tanaydhavate/ODT2026-CapstoneProjectName-Tanay/Media/Week1/WhatsApp Image 2026-04-22 at 2.16.44 AM (1).jpeg

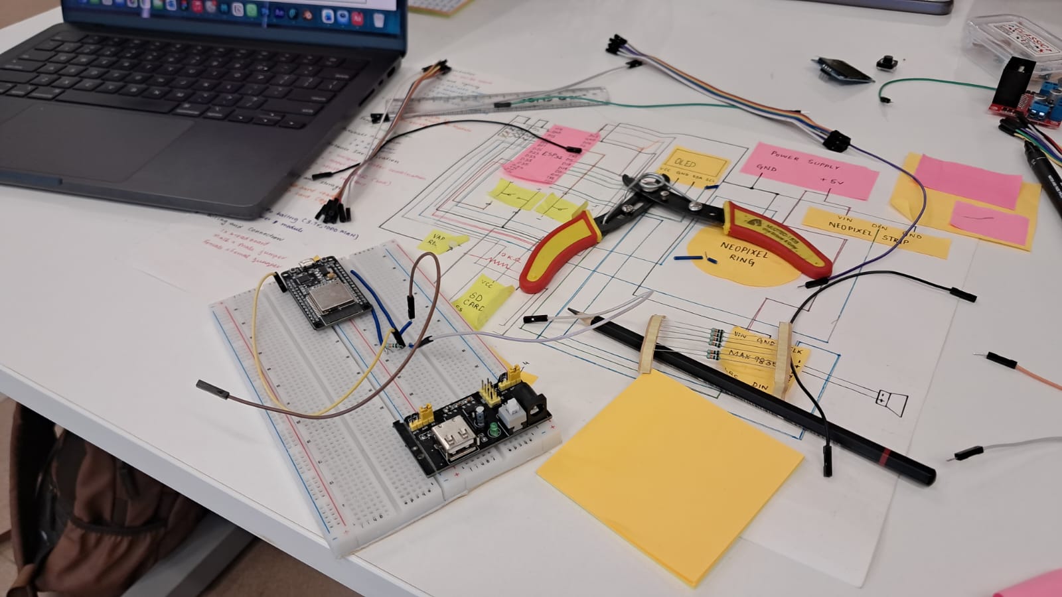
Media/Week1/WhatsApp Image 2026-04-22 at 2.16.44 AM (1).jpeg
