tanaydhavate/ODT2026-CapstoneProjectName-Tanay/Media/Week2/WhatsApp Image 2026-04-22 at 2.16.32 AM (1).jpeg

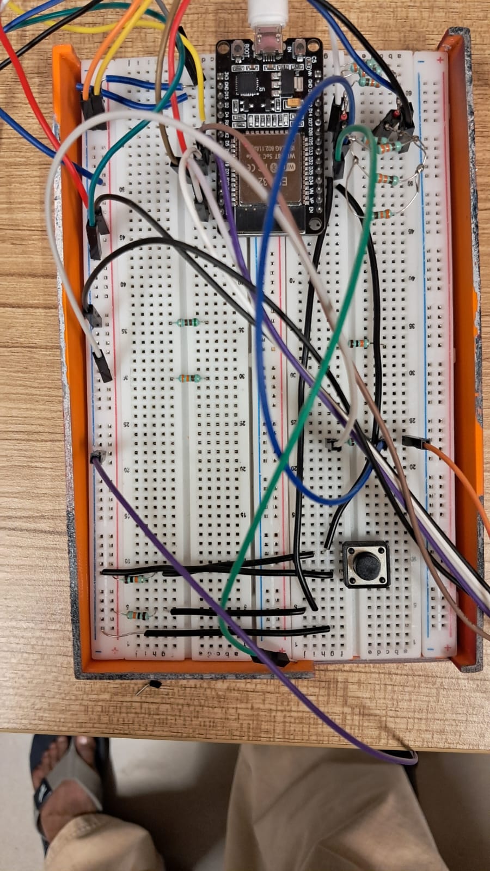
Media/Week2/WhatsApp Image 2026-04-22 at 2.16.32 AM (1).jpeg
