tanaydhavate/ODT2026-CapstoneProjectName-Tanay/Software Details/All codes/gengar working .py

import gc
import os
import sdcard
import framebuf

from time import sleep_ms, sleep
from machine import Pin, SPI, I2C, I2S
from neopixel import NeoPixel
from SH1106 import SH1106_I2C

gc.collect()

SD_CS_PIN       = 5
SD_SCK_PIN      = 18
SD_MOSI_PIN     = 23
SD_MISO_PIN     = 19

NEOPIXEL_PIN    = 4
NUM_LEDS        = 16

OLED_SCL_PIN    = 22
OLED_SDA_PIN    = 21
OLED_ADDR       = 0x3C
OLED_W          = 128
OLED_H          = 64

I2S_SCK_PIN     = 26
I2S_WS_PIN      = 25
I2S_SD_PIN      = 27

FRAME_WIDTH     = 128
FRAME_HEIGHT    = 64
FRAME_SIZE      = 1024

AUDIO_RATE      = 8000
AUDIO_BUF_SIZE  = 4096
MONO_BUF_SIZE   = 512

FRAME_FILE      = "/sd/gengar.bin"
WAV_FILE        = "/sd/gengar.wav"

DARK_PURPLE     = (250, 0, 250)
LIGHT_PURPLE    = (100, 0, 250)

def init_sd():
    cs = Pin(SD_CS_PIN, Pin.OUT)
    cs.value(1)
    sleep_ms(300)
    spi = SPI(
        1,
        baudrate=100000,
        polarity=0,
        phase=0,
        sck=Pin(SD_SCK_PIN),
        mosi=Pin(SD_MOSI_PIN),
        miso=Pin(SD_MISO_PIN)
    )
    sleep_ms(200)
    sd = sdcard.SDCard(spi, cs)
    os.mount(sd, "/sd")
    print("SD OK")
    return spi, sd


def init_neopixel():
    pin = Pin(NEOPIXEL_PIN, Pin.OUT, value=0)
    strip = NeoPixel(pin, NUM_LEDS)
    strip.fill((0, 0, 0))
    strip.write()
    sleep_ms(50)
    return strip


def show_gengar_colors(strip):
    for i in range(4):
        strip[i] = DARK_PURPLE
    for i in range(4, 8):
        strip[i] = LIGHT_PURPLE
    strip.write()


def clear_strip(strip):
    strip.fill((0, 0, 0))
    strip.write()


def load_frames(path):
    frames = []
    count = 0
    with open(path, "rb") as f:
        while True:
            data = f.read(FRAME_SIZE)
            if len(data) < FRAME_SIZE:
                break
            frames.append(bytearray(data))
            count += 1
            if count > 30:  # cap frames to avoid SD/memory stress
                break
    return frames


def init_oled():
    i2c = I2C(0, scl=Pin(OLED_SCL_PIN), sda=Pin(OLED_SDA_PIN))
    oled = SH1106_I2C(OLED_W, OLED_H, i2c, addr=OLED_ADDR)
    oled.fill(0)
    oled.invert(True)
    oled.show()
    return i2c, oled


def draw_info(oled):
    oled.text("Gengar",     78,  0, 0)
    oled.text("----------", 70,  9, 0)
    oled.text("Ghost",      78, 18, 0)
    oled.text("Poison",     78, 27, 0)
    oled.text("----------", 70, 36, 0)
    oled.text("Kanto",      78, 45, 0)
    oled.text("1.5m 41kg",  70, 55, 0)


def draw_frame(oled, frame_bytes):
    fb = framebuf.FrameBuffer(frame_bytes, FRAME_WIDTH, FRAME_HEIGHT, framebuf.MONO_HLSB)
    oled.fill(1)
    oled.blit(fb, 0, 0)
    draw_info(oled)
    oled.show()


def init_audio():
    return I2S(
        0,
        sck=Pin(I2S_SCK_PIN),
        ws=Pin(I2S_WS_PIN),
        sd=Pin(I2S_SD_PIN),
        mode=I2S.TX,
        bits=16,
        format=I2S.MONO,
        rate=AUDIO_RATE,
        ibuf=AUDIO_BUF_SIZE
    )


spi = None
sd = None
np = None
oled = None
audio = None
wav = None

try:
    spi, sd = init_sd()

    np = init_neopixel()
    show_gengar_colors(np)      # set once, never changed again

    frames = load_frames(FRAME_FILE)
    n_frames = len(frames)
    print("Frames:", n_frames)

    gc.collect()
    print("Free RAM:", gc.mem_free())

    if n_frames == 0:
        raise Exception("No frames found in gengar.bin")

    # Extra delay to stabilize SD card after mounting (fixes 'timeout waiting for response')
    sleep(1)

    i2c, oled = init_oled()

    gc.collect()
    sleep_ms(500)
    audio = init_audio()
    mono_buf = bytearray(MONO_BUF_SIZE)

    wav = open(WAV_FILE, "rb")
    wav.seek(44)

    print("Playing Gengar with constant NeoPixel...")

    frame_i = 0
    loop_count = 0

    while True:
        num = wav.readinto(mono_buf)
        if num == 0:
            break

        if num < MONO_BUF_SIZE:
            for i in range(num, MONO_BUF_SIZE):
                mono_buf[i] = 0

        audio.write(mono_buf)

        if loop_count % 6 == 0:
            if n_frames > 0:
                draw_frame(oled, frames[frame_i % n_frames])
                frame_i += 1

        loop_count += 1

    print("Playback done")

except Exception as e:
    print("ERROR:", e)

finally:
    try:
        if wav:
            wav.close()
    except:
        pass

    try:
        if audio:
            audio.deinit()
    except:
        pass

    try:
        if np:
            clear_strip(np)
            sleep_ms(50)
    except:
        pass

    try:
        if oled:
            oled.fill(0)
            oled.show()
    except:
        pass

    gc.collect()
    print("Gengar complete!")
